jue89/homie/devices/switchy/emsd/21-02/housing/3back.stl

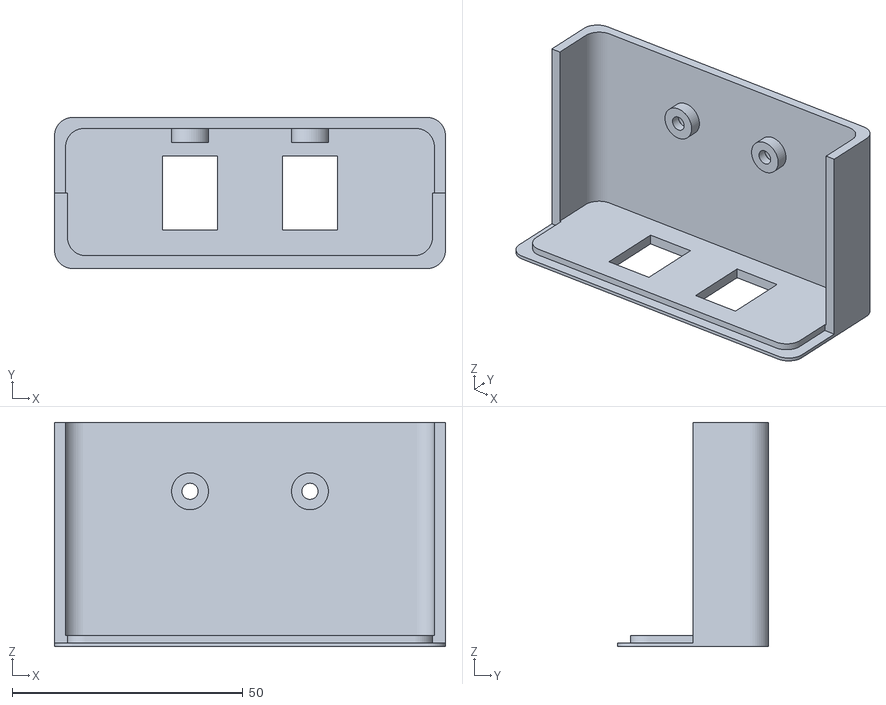
[picture p15: CAD file, 2021-03-21]
devices/switchy/emsd/21-02/housing/3back.stl
84.8 x 32.8 x 48.6
