jue89/homie/devices/switchy/emsd/21-02/housing/5back.stl

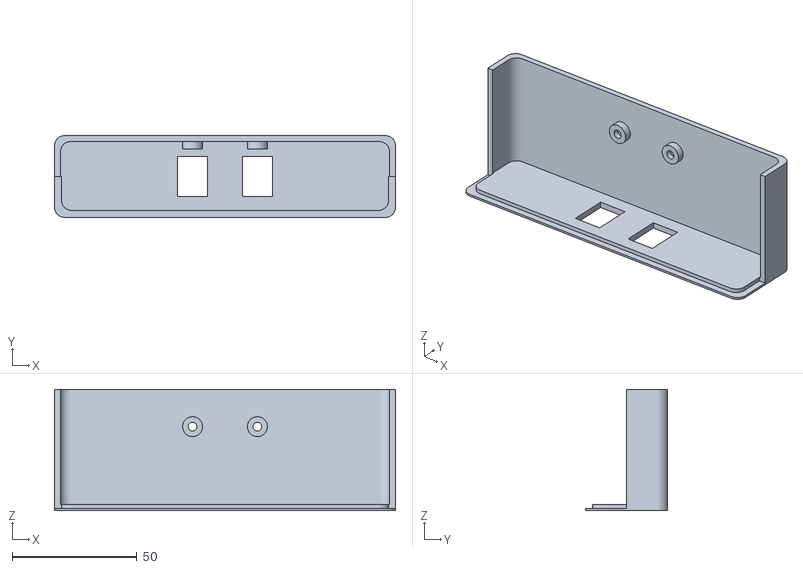
[picture p16: CAD file, 2021-03-21]
devices/switchy/emsd/21-02/housing/5back.stl
136.8 x 32.8 x 48.6
